Fabiancrg/acw02_zb/main/esp_zb_hvac.h

/*
 * SPDX-FileCopyrightText: 2024 Espressif Systems (Shanghai) CO LTD
 *
 * SPDX-License-Identifier: LicenseRef-Included
 *
 * Zigbee HVAC Thermostat Header
 */

#ifndef ESP_ZB_HVAC_H
#define ESP_ZB_HVAC_H

#include "esp_zigbee_core.h"
#include "hvac_driver.h"
#include "zcl_utility.h"

/* Zigbee configuration */
#define INSTALLCODE_POLICY_ENABLE       false                                /* enable the install code policy for security */
#define ED_AGING_TIMEOUT                ESP_ZB_ED_AGING_TIMEOUT_64MIN        /* aging timeout of device */
#define ED_KEEP_ALIVE                   3000                                 /* 3000 millisecond */
#define HA_ESP_HVAC_ENDPOINT            1                                    /* HVAC thermostat endpoint */
#define HA_ESP_ECO_ENDPOINT             2                                    /* Eco mode switch endpoint */
#define HA_ESP_SWING_ENDPOINT           3                                    /* Swing mode switch endpoint */
#define HA_ESP_DISPLAY_ENDPOINT         4                                    /* Display control switch endpoint */
#define HA_ESP_NIGHT_ENDPOINT           5                                    /* Night mode switch endpoint */
#define HA_ESP_PURIFIER_ENDPOINT        6                                    /* Purifier switch endpoint */
#define HA_ESP_CLEAN_ENDPOINT           7                                    /* Clean status binary sensor endpoint */
#define HA_ESP_MUTE_ENDPOINT            8                                    /* Mute switch endpoint */
#define HA_ESP_ERROR_ENDPOINT           9                                    /* Error/diagnostics binary sensor endpoint */
#define ESP_ZB_PRIMARY_CHANNEL_MASK     ESP_ZB_TRANSCEIVER_ALL_CHANNELS_MASK /* Zigbee primary channel mask use in the example */

/* Button configuration */
#define ESP_INTR_FLAG_DEFAULT 0

/* Basic manufacturer information */
#define ESP_MANUFACTURER_NAME "\x14""Custom devices (DiY)"      /* Customized manufacturer name */
#define ESP_MODEL_IDENTIFIER "\x07""acw02-z"         /* Customized model identifier */

#define ESP_ZB_ZED_CONFIG()                                         \
    {                                                               \
        .esp_zb_role = ESP_ZB_DEVICE_TYPE_ED,                       \
        .install_code_policy = INSTALLCODE_POLICY_ENABLE,           \
        .nwk_cfg.zed_cfg = {                                        \
            .ed_timeout = ED_AGING_TIMEOUT,                         \
            .keep_alive = ED_KEEP_ALIVE,                            \
        },                                                          \
    }

#define ESP_ZB_DEFAULT_RADIO_CONFIG()                           \
    {                                                           \
        .radio_mode = ZB_RADIO_MODE_NATIVE,                     \
    }

#define ESP_ZB_DEFAULT_HOST_CONFIG()                            \
    {                                                           \
        .host_connection_mode = ZB_HOST_CONNECTION_MODE_NONE,   \
    }

#endif
